mokjpn/waveshare-esp32-weather-epaper/include/app_secrets.example.h

#pragma once

// Copy this file to app_secrets.h and fill in real values.

#define APP_WIFI_SSID "YOUR_WIFI_SSID"
#define APP_WIFI_PASSWORD "YOUR_WIFI_PASSWORD"

#define APP_RELAY_BASE_URL "http://your-server.example.com:8080"

#define APP_MQTT_HOST "192.168.1.10"
#define APP_MQTT_PORT 1883
#define APP_MQTT_USERNAME ""
#define APP_MQTT_PASSWORD ""
#define APP_MQTT_TOPIC_BASE "devices/waveshare-esp32-weather-epaper"
